mjdigit/tps43-ek/images/BottomPlate.png

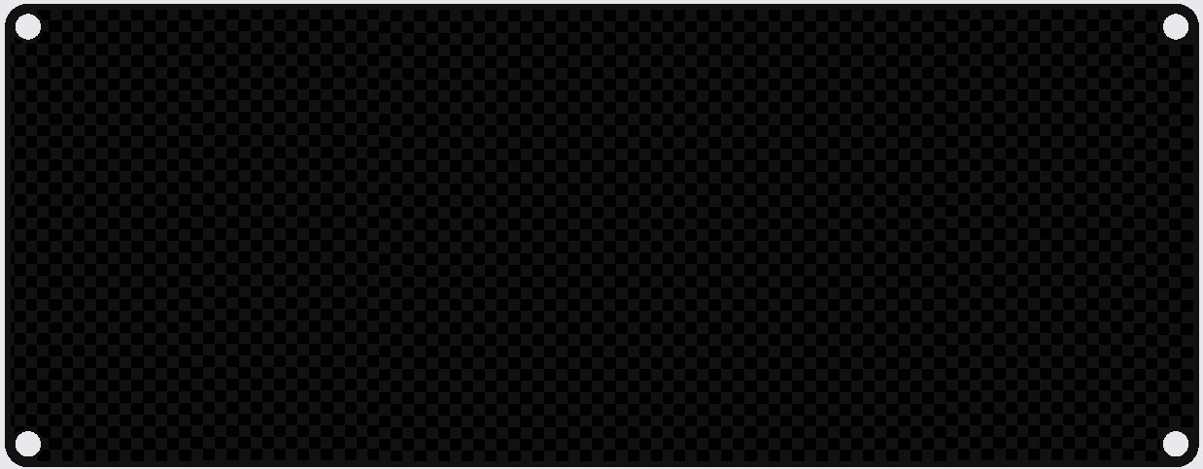
images/BottomPlate.png
