mjdigit/tps43-ek/images/MainPlate.png

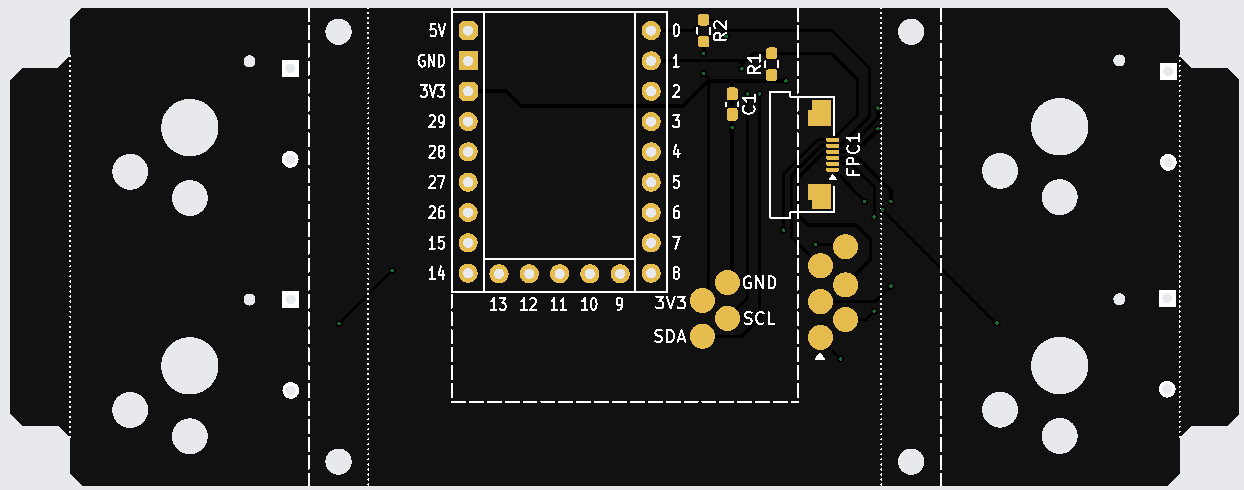
images/MainPlate.png
