mjdigit/tps43-ek/images/TopPlate.png

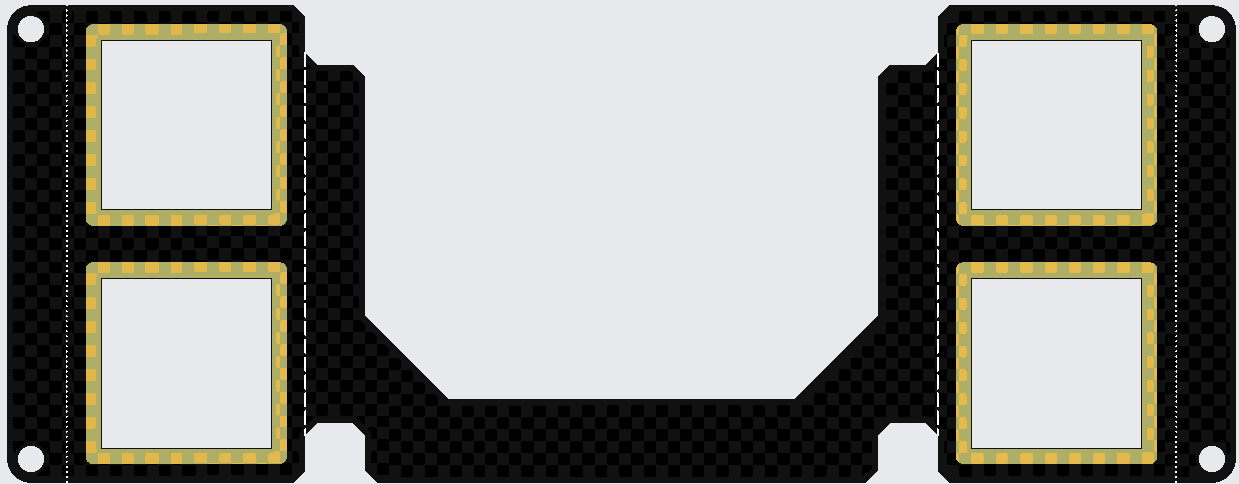
images/TopPlate.png
