mjdigit/tps43-ek/images/TouchpadMountPlate.png

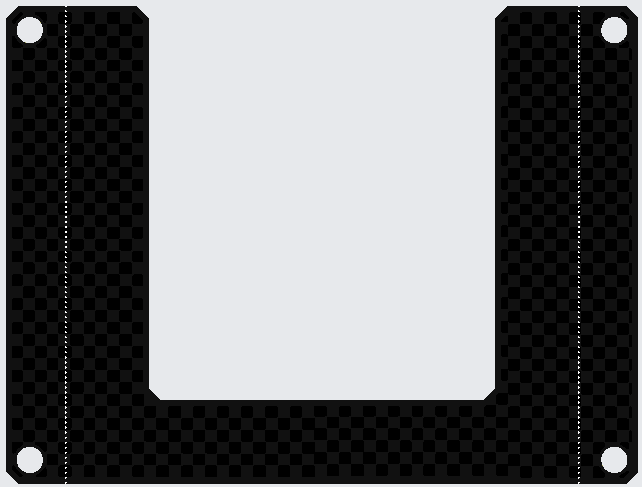
images/TouchpadMountPlate.png
